linorobot/ros_dwm1000/scripts/localize.py

#!/usr/bin/env python

'''
 Copyright (c) 2016, Juan Jimeno

 All rights reserved.

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
 THIS SOFTWARE IS PROVIDED BY THE COPYRIGHT HOLDERS AND CONTRIBUTORS "AS IS"
 AND ANY EXPRESS OR IMPLIED WARRANTIES, INCLUDING, BUT NOT LIMITED TO, THE
 IMPLIED WARRANTIES OF MERCHANTABILITY AND FITNESS FOR A PARTICULAR PURPOSE
 ARE DISCLAIMED. IN NO EVENT SHALL THE COPYRIGHT OWNER OR CONTRIBUTORS BE
 LIABLE FOR ANY DIRECT, INDIRECT, INCIDENTAL, SPECIAL, EXEMPLARY, OR
 CONSEQUENTIAL DAMAGES (INCLUDING, BUT NOT LIMITED TO, PROCUREMENT OF
 SUBSTITUTE GOODS OR SERVICES; LOSS OF USE, DATA, OR PROFITS; OR BUSINESS
 INTERRUPTION) HOWEVER CAUSED AND ON ANY THEORY OF LIABILITY, WHETHER IN
 CONTRACT, STRICT LIABILITY, OR TORT (INCLUDING NEGLIGENCE OR OTHERWISE)
 ARISING IN ANY WAY OUT OF THE USE OF THIS SOFTWARE, EVEN IF ADVISED OF THE
 POSSIBILITY OF SUCH DAMAGE.
'''

import rospy
import tf
import localization as lx
import serial

def get_transform(id):
    try:
        (trans,rot) = listener.lookupTransform('/map', id, rospy.Time(0))
        return trans
    except (tf.LookupException, tf.ConnectivityException, tf.ExtrapolationException):
        pass

def get_tag_location(anchors, ranges, transforms):
    P = lx.Project(mode="3D",solver="LSE")

    #define anchor locations
    for i in range(REQ_ANCHOR):
        P.add_anchor(anchors[i], transforms[i])
    t, label = P.add_target()

    #define anchor ranges
    for i in range(REQ_ANCHOR):
        t.add_measure(anchors[i], ranges[i])

    P.solve()
    B = t.loc
    return {'x':B.x, 'y':B.y, 'z':B.z}

def is_listed(anchors, id):
    for anchor in anchors:
        if anchor == id:
            return True
        else:
            pass

def get_serial_data():
    start = ser.read()
    # return ser.readline().strip('$\r\n').split(',')
    # expected data from the serial port is: $<anchor_id>,<range in cm>,\r\n
    if start == '$':
        parsed_data = ser.readline().strip('\r\n').split(',')
        # anchor id is stored in index 0 - parsed_data[0]
        # range is stored in index 1 - parsed_data[1]
        return parsed_data
    else:
        return None

if __name__ == '__main__':

    rospy.init_node('ros_dwm1000')
    listener = tf.TransformListener()
    start_time = rospy.get_time()

    #create rosparameters
    MIN_RANGE = rospy.get_param('/ros_dwm1000/min_range', 0.5)
    MAX_RANGE = rospy.get_param('/ros_dwm1000/max_range', 10.0)
    REQ_ANCHOR = rospy.get_param('/ros_dwm1000/req_anchor', 3)
    FRAME_ID = rospy.get_param('/ros_dwm1000/frame_id', 'uwb_tag')
    SERIAL_PORT = rospy.get_param('/ros_dwm1000/serial_port', '/dev/ttyUSB0')

    #rosparam logs just to make sure parameters kicked in
    rospy.loginfo("%s is %s", rospy.resolve_name('/ros_dwm1000/min_range'), MIN_RANGE)
    rospy.loginfo("%s is %s", rospy.resolve_name('/ros_dwm1000/max_range'), MAX_RANGE)
    rospy.loginfo("%s is %s", rospy.resolve_name('/ros_dwm1000/req_anchor'), REQ_ANCHOR)
    rospy.loginfo("%s is %s", rospy.resolve_name('/ros_dwm1000/frame_id'), FRAME_ID)
    rospy.loginfo("%s is %s", rospy.resolve_name('/ros_dwm1000/serial_port'), SERIAL_PORT)

    ser = serial.Serial(SERIAL_PORT, 115200)
    ser.timeout = None
    rospy.loginfo("Connected to %s", ser.portstr)

    #lists to store anchors found
    ranges = []
    anchors = []
    transforms = []
    anchors_found = 0

    while not rospy.is_shutdown():
        #get the stream of data from the tag through the serial port
        parsed_data = get_serial_data()

        # print parsed_data
        if None != parsed_data:
            #check if the current range is within specified distance
            if MIN_RANGE < float(parsed_data[1]) < MAX_RANGE:
                #append respective arrays of the anchor found
                #list of anchor IDs found
                anchors.append(parsed_data[0])
                #list of distance between tag and anchors found
                ranges.append(parsed_data[1])
                #list of static TFs of the anchors found.
                transforms.append(get_transform(parsed_data[0]))
                anchors_found += 1

        #perform trilateration once enough anchors have been found
        if anchors_found == REQ_ANCHOR:
            #do trilateration
            pos = get_tag_location(anchors,ranges,transforms)

            #broadcast the transform
            br = tf.TransformBroadcaster()
            br.sendTransform((pos['x'], pos['y'], pos['z']),
                            tf.transformations.quaternion_from_euler(0, 0, 0),
                            rospy.Time.now(),
                            FRAME_ID,
                            "map")

            #TODO: Publish pos as geometry_msgs/PoseWithCovarianceStamped for EKF and only broadcast TF as an option.

            # clear lists once trilateration is done for the next cycle
            anchors_found = 0
            ranges = []
            transforms = []
            anchors = []
